beel1/15khzvgatester/src/VGA_output_multi/screenFont.h

// bit patterns for the CP437 font, ROTATED, INVERTED

// To save rendering time, they are ordered by line (ie. line 1, line 2) and then 
//  indexed by character.

const byte screen_font [8] [256] PROGMEM = {
// Row 1
 { 
  0xFF, 0xC0, 0xC0, 0xC9, 0xF7, 0xE3, 0xF7, 0xFF, 0x80, 0xFF, 0x80, 0xF8, 0xE1, 0xE0, 0xFA, 0x5F, 
  0xBF, 0xFE, 0xF3, 0xCC, 0xC0, 0xE0, 0xFF, 0xF3, 0xF3, 0xF3, 0xFF, 0xFF, 0xFF, 0xFF, 0xFF, 0xFF, 
  0xFF, 0xE7, 0xC9, 0xC9, 0xE7, 0xFF, 0xE3, 0xCF, 0xF3, 0xCF, 0xFF, 0xFF, 0xFF, 0xFF, 0xFF, 0xFC, 
  0xC3, 0xE7, 0xC3, 0xC3, 0xF1, 0x81, 0xC3, 0x81, 0xC3, 0xC3, 0xFF, 0xFF, 0xF3, 0xFF, 0xCF, 0xC3, 
  0xC1, 0xE7, 0x81, 0xE1, 0x83, 0x80, 0x80, 0xC1, 0x99, 0xC3, 0xF0, 0x8C, 0x9F, 0x9C, 0x9C, 0xE3, 
  0x81, 0xC3, 0x81, 0xC3, 0x81, 0x99, 0x99, 0x9C, 0x9C, 0x99, 0x80, 0xC3, 0x9F, 0xC3, 0xF7, 0xFF, 
  0xE7, 0xFF, 0x8F, 0xFF, 0xF1, 0xFF, 0xE3, 0xFF, 0x8F, 0xE7, 0xF9, 0x8F, 0xC7, 0xFF, 0xFF, 0xFF, 
  0xFF, 0xFF, 0xFF, 0xFF, 0xF7, 0xFF, 0xFF, 0xFF, 0xFF, 0xFF, 0xFF, 0xF1, 0xF3, 0x8F, 0xC4, 0xFF, 
  0xC3, 0xFF, 0xF1, 0xC0, 0x99, 0x8F, 0xE7, 0xFF, 0xC0, 0x99, 0x8F, 0x99, 0xC1, 0x8F, 0x9C, 0xE7, 
  0xF1, 0xFF, 0xE0, 0xC3, 0xFF, 0xFF, 0xC3, 0xFF, 0xFF, 0x9E, 0x99, 0xF3, 0xE3, 0x99, 0x83, 0xF8, 
  0xF1, 0xE3, 0xFF, 0xFF, 0xFF, 0x81, 0xE1, 0xE3, 0xE7, 0xFF, 0xFF, 0x9E, 0x9E, 0xF3, 0xFF, 0xFF, 
  0xEE, 0xD5, 0x92, 0xF3, 0xF3, 0xF3, 0xE4, 0xFF, 0xFF, 0xE4, 0xE4, 0xFF, 0xE4, 0xE4, 0xF3, 0xFF, 
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
  0xFF, 0x9F, 0xFF, 0xFF, 0xFF, 0xFF, 0x9F, 0xFF, 0x81, 0xFF, 0xFF, 0xFF, 0xFF, 0x9F, 0xFF, 0xFF, 
  0xFF, 0xFF, 0xFF, 0xFF, 0xF3, 0xC7, 0xFF, 0xFF, 0xFF, 0xFF, 0xFF, 0xF1, 0xFF, 0xFF, 0xFF, 0xFF, 
  }, 

};  //  end of screen_font
