beel1/15khzvgatester/src/VGA_output_multi/screenFontST.h

// bit patterns for the 8x8 system font, ROTATED, INVERTED

// To save rendering time, they are ordered by line (ie. line 1, line 2) and then 
//  indexed by character.

const byte screen_font [8] [256] PROGMEM = {
// Row 1
 { 
  0xFF, 0xE7, 0xC3, 0xE7, 0xE7, 0xC3, 0x00, 0x18, 0xFE, 0x81, 0xE7, 0xE7, 0x0F, 0x0F, 0xFA, 0x5F, 
  0x83, 0xF9, 0x83, 0x83, 0x39, 0x83, 0x83, 0x83, 0x83, 0x83, 0xFF, 0x87, 0xF8, 0x0F, 0xEE, 0xFB, 
  0xFF, 0xE7, 0x99, 0xFF, 0xE7, 0xFF, 0xC7, 0xE7, 0xF1, 0x8F, 0xFF, 0xFF, 0xFF, 0xFF, 0xFF, 0xFD, 
  0xC3, 0xE7, 0xC3, 0x81, 0xF3, 0x81, 0xC3, 0x81, 0xC3, 0xC3, 0xFF, 0xFF, 0xF9, 0xFF, 0x9F, 0xC3, 
  0xC3, 0xE7, 0x83, 0xC3, 0x87, 0x81, 0x81, 0xC1, 0x99, 0xC3, 0xF9, 0x99, 0x9F, 0x39, 0x99, 0xC3, 
  0x83, 0xC3, 0x83, 0xC3, 0x81, 0x99, 0x99, 0x39, 0x99, 0x99, 0x81, 0xE1, 0xBF, 0x87, 0xEF, 0xFF, 
  0xFF, 0xFF, 0x9F, 0xFF, 0xF9, 0xFF, 0xE3, 0xFF, 0x9F, 0xE7, 0xE7, 0x9F, 0xC7, 0xFF, 0xFF, 0xFF, 
  0xFF, 0xFF, 0xFF, 0xFF, 0xFF, 0xFF, 0xFF, 0xFF, 0xFF, 0xFF, 0xFF, 0xF1, 0xE7, 0x8F, 0xFF, 0xFF, 
  0xFF, 0x99, 0xF3, 0xE7, 0x99, 0xCF, 0xE7, 0xFF, 0xE7, 0x99, 0xCF, 0x99, 0xE7, 0x9F, 0x99, 0xE7, 
  0xF3, 0xFF, 0xC0, 0xE7, 0x99, 0xCF, 0xE7, 0xCF, 0x99, 0x99, 0x99, 0xE7, 0xE3, 0x99, 0xE3, 0xE1, 
  0xF3, 0xF3, 0xF3, 0xF3, 0xCB, 0xCB, 0xFF, 0xFF, 0xFF, 0xFF, 0xFF, 0x39, 0x39, 0xFF, 0xE4, 0x27, 
  0xCB, 0xCB, 0xFD, 0xFF, 0xFF, 0x80, 0xCF, 0xCB, 0xCB, 0x99, 0xF3, 0xFF, 0x85, 0x81, 0x81, 0x0E, 
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
  0xFF, 0x9F, 0x07, 0xB7, 0xFF, 0xFF, 0x3F, 0xEF, 0xC3, 0xFF, 0xFF, 0xFF, 0x9F, 0xEF, 0xFF, 0xFF, 
  0xFF, 0xFF, 0xFF, 0xFF, 0xE7, 0xFF, 0xFF, 0xFF, 0xFF, 0xFF, 0xFF, 0xFF, 0xFF, 0xFF, 0xFF, 0xFF, 
  }, 

};  //  end of screen_font
